folfy/tinylight/tiny_software/tinyLight/Form1.h

#pragma once
;
namespace tinyLight {

	using namespace System;
	using namespace System::ComponentModel;
	using namespace System::Collections;
	using namespace System::Windows::Forms;
	using namespace System::Data;
	using namespace System::Drawing;

	/// <summary>
	/// Zusammenfassung für Form1
	/// </summary>
	public ref class Form1 : public System::Windows::Forms::Form
	{
	public:
		Form1(void)
		{
			InitializeComponent();
			//
			//TODO: Konstruktorcode hier hinzufügen.
			//
		}

	protected:
		/// <summary>
		/// Verwendete Ressourcen bereinigen.
		/// </summary>
		~Form1()
		{
			if (components)
			{
				delete components;
			}
		}



	private: System::Windows::Forms::TabControl^  tabControl1;
	private: System::Windows::Forms::TabPage^  tabPage1;
	private: System::Windows::Forms::TabPage^  tabPage2;
	private: System::Windows::Forms::TreeView^  treeView1;
	private: System::Windows::Forms::StatusStrip^  statusStrip1;
	private: System::Windows::Forms::Button^  button1;
	private: System::Windows::Forms::ComboBox^  comboBox1;
	private: System::Windows::Forms::Label^  label1;


	protected: 

	protected: 





	private: System::ComponentModel::IContainer^  components;
	protected: 

	private:
		/// <summary>
		/// Erforderliche Designervariable.
		/// </summary>


#pragma region Windows Form Designer generated code
		/// <summary>
		/// Erforderliche Methode für die Designerunterstützung.
		/// Der Inhalt der Methode darf nicht mit dem Code-Editor geändert werden.
		/// </summary>
		void InitializeComponent(void)
		{
			System::ComponentModel::ComponentResourceManager^  resources = (gcnew System::ComponentModel::ComponentResourceManager(Form1::typeid));
			this->tabControl1 = (gcnew System::Windows::Forms::TabControl());
			this->tabPage1 = (gcnew System::Windows::Forms::TabPage());
			this->label1 = (gcnew System::Windows::Forms::Label());
			this->comboBox1 = (gcnew System::Windows::Forms::ComboBox());
			this->button1 = (gcnew System::Windows::Forms::Button());
			this->tabPage2 = (gcnew System::Windows::Forms::TabPage());
			this->treeView1 = (gcnew System::Windows::Forms::TreeView());
			this->statusStrip1 = (gcnew System::Windows::Forms::StatusStrip());
			this->tabControl1->SuspendLayout();
			this->tabPage1->SuspendLayout();
			this->SuspendLayout();
			// 
			// tabControl1
			// 
			this->tabControl1->Controls->Add(this->tabPage1);
			this->tabControl1->Controls->Add(this->tabPage2);
			this->tabControl1->Location = System::Drawing::Point(111, 12);
			this->tabControl1->Name = L"tabControl1";
			this->tabControl1->SelectedIndex = 0;
			this->tabControl1->Size = System::Drawing::Size(311, 389);
			this->tabControl1->TabIndex = 2;
			// 
			// tabPage1
			// 
			this->tabPage1->Controls->Add(this->label1);
			this->tabPage1->Controls->Add(this->comboBox1);
			this->tabPage1->Controls->Add(this->button1);
			this->tabPage1->Location = System::Drawing::Point(4, 22);
			this->tabPage1->Name = L"tabPage1";
			this->tabPage1->Padding = System::Windows::Forms::Padding(3);
			this->tabPage1->Size = System::Drawing::Size(303, 363);
			this->tabPage1->TabIndex = 0;
			this->tabPage1->Text = L"tabPage1";
			this->tabPage1->UseVisualStyleBackColor = true;
			// 
			// label1
			// 
			this->label1->AutoSize = true;
			this->label1->Location = System::Drawing::Point(93, 11);
			this->label1->Name = L"label1";
			this->label1->Size = System::Drawing::Size(35, 13);
			this->label1->TabIndex = 2;
			this->label1->Text = L"label1";
			// 
			// comboBox1
			// 
			this->comboBox1->FormattingEnabled = true;
			this->comboBox1->Location = System::Drawing::Point(7, 36);
			this->comboBox1->Name = L"comboBox1";
			this->comboBox1->Size = System::Drawing::Size(121, 21);
			this->comboBox1->TabIndex = 1;
			this->comboBox1->SelectedIndexChanged += gcnew System::EventHandler(this, &Form1::comboBox1_SelectedIndexChanged);
			// 
			// button1
			// 
			this->button1->Location = System::Drawing::Point(6, 6);
			this->button1->Name = L"button1";
			this->button1->Size = System::Drawing::Size(75, 23);
			this->button1->TabIndex = 0;
			this->button1->Text = L"Scan";
			this->button1->UseVisualStyleBackColor = true;
			this->button1->Click += gcnew System::EventHandler(this, &Form1::button1_Click_1);
			// 
			// tabPage2
			// 
			this->tabPage2->Location = System::Drawing::Point(4, 22);
			this->tabPage2->Name = L"tabPage2";
			this->tabPage2->Padding = System::Windows::Forms::Padding(3);
			this->tabPage2->Size = System::Drawing::Size(303, 363);
			this->tabPage2->TabIndex = 1;
			this->tabPage2->Text = L"tabPage2";
			this->tabPage2->UseVisualStyleBackColor = true;
			// 
			// treeView1
			// 
			this->treeView1->Location = System::Drawing::Point(7, 11);
			this->treeView1->Name = L"treeView1";
			this->treeView1->Size = System::Drawing::Size(98, 390);
			this->treeView1->TabIndex = 3;
			// 
			// statusStrip1
			// 
			this->statusStrip1->Location = System::Drawing::Point(0, 413);
			this->statusStrip1->Name = L"statusStrip1";
			this->statusStrip1->Size = System::Drawing::Size(434, 22);
			this->statusStrip1->TabIndex = 1;
			this->statusStrip1->Text = L"statusStrip1";
			// 
			// Form1
			// 
			this->AutoScaleDimensions = System::Drawing::SizeF(6, 13);
			this->AutoScaleMode = System::Windows::Forms::AutoScaleMode::Font;
			this->ClientSize = System::Drawing::Size(434, 435);
			this->Controls->Add(this->treeView1);
			this->Controls->Add(this->tabControl1);
			this->Controls->Add(this->statusStrip1);
			this->Icon = (cli::safe_cast<System::Drawing::Icon^  >(resources->GetObject(L"$this.Icon")));
			this->MaximizeBox = false;
			this->MinimumSize = System::Drawing::Size(450, 473);
			this->Name = L"Form1";
			this->Text = L"tinyLight";
			this->tabControl1->ResumeLayout(false);
			this->tabPage1->ResumeLayout(false);
			this->tabPage1->PerformLayout();
			this->ResumeLayout(false);
			this->PerformLayout();

		}
#pragma endregion
private: System::Void button1_Click_1(System::Object^  sender, System::EventArgs^  e) {
			 
			label1->Text=Serial::getDevice();
 }
private: System::Void comboBox1_SelectedIndexChanged(System::Object^  sender, System::EventArgs^  e) {
		 }
};
}
