folfy/tinylight/tiny_firmware/tinylight/src/misc_adc.h

/*
 * misc_adc.h
 *
 * Created: 21.04.2014 20:36:46
 *  Author: Folfy
 */ 


#ifndef MISC_ADC_H_
#define MISC_ADC_H_

/* ADC */

extern volatile adc_sample measure;

void adc_init(void);

void get_max_reset(uint_fast16_t *u_min, uint_fast16_t *i_max);

/* Sleep */

void power_down(void);

extern Bool volatile sleeping;

#endif /* MISC_ADC_H_ */
