folfy/tinylight/tiny_software/tinyLight/AssemblyInfo.cpp

#include "stdafx.h"

using namespace System;
using namespace System::Reflection;
using namespace System::Runtime::CompilerServices;
using namespace System::Runtime::InteropServices;
using namespace System::Security::Permissions;

//
// Allgemeine Informationen über eine Assembly werden über die folgenden
// Attribute gesteuert. Ändern Sie diese Attributwerte, um die Informationen zu ändern,
// die mit einer Assembly verknüpft sind.
//
[assembly:AssemblyTitleAttribute("tinyLight")];
[assembly:AssemblyDescriptionAttribute("")];
[assembly:AssemblyConfigurationAttribute("")];
[assembly:AssemblyCompanyAttribute("")];
[assembly:AssemblyProductAttribute("tinyLight")];
[assembly:AssemblyCopyrightAttribute("Copyright (c)  2014")];
[assembly:AssemblyTrademarkAttribute("")];
[assembly:AssemblyCultureAttribute("")];

//
// Versionsinformationen für eine Assembly bestehen aus den folgenden vier Werten:
//
//      Hauptversion
//      Nebenversion
//      Buildnummer
//      Revision
//
// Sie können alle Werte angeben oder für die Revisions- und Buildnummer den Standard
// übernehmen, indem Sie "*" eingeben:

[assembly:AssemblyVersionAttribute("1.0.*")];

[assembly:ComVisible(false)];

[assembly:CLSCompliantAttribute(true)];

[assembly:SecurityPermission(SecurityAction::RequestMinimum, UnmanagedCode = true)];
