folfy/tinylight/tiny_bootloader/common/services/usb/class/dfu_flip/device/bootloader/xmega/main.c

/**
 * \file
 *
 * \brief Main functions
 *
 * Copyright (c) 2011 - 2012 Atmel Corporation. All rights reserved.
 *
 * \asf_license_start
 *
 * \page License
 *
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
 * 3. The name of Atmel may not be used to endorse or promote products derived
 *    from this software without specific prior written permission.
 *
 * 4. This software may only be redistributed and used in connection with an
 *    Atmel microcontroller product.
 *
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
 * \asf_license_stop
 *
 */

#include <asf.h>
#include "conf_usb.h"
#include "led.h"

/*! \brief Main function. Execution starts here.
 */
int main(void)
{
	// Map interrupt vectors table in bootloader section
	ccp_write_io((uint8_t*)&PMIC.CTRL, PMIC_IVSEL_bm | PMIC_LOLVLEN_bm
			| PMIC_MEDLVLEN_bm | PMIC_HILVLEN_bm);

	sysclk_init();
	cpu_irq_enable();
        led_on();
	// Start USB stack to authorize VBus monitoring
	udc_start();

	udc_attach();
	while (true) {
	}
}


/**
 * \mainpage ASF USB Device DFU
 *
 * \section intro Introduction
 * This application is the official Atmel USB DFU bootloader for XMEGA.
 *
 * A USB DFU bootloader guide is proposed for all AVR XMEGA parts with USB interface:
 *
 * \section files Application Files
 * The specific files of application are:
 * - main.c: the main file to start clock and USB DFU Device.
 * - specific linker script
 * - specific optimized codes to fit with boot section size
 */
